pedrorovi/rc-car/platformio/test/embedded/components/test_bt/test_main.cpp

#include <unity.h>

#include <test_utils.h>
#include <tests.h>

int main(void) {
    UNITY_BEGIN();
    RUN_TEST(test_setup);
    RUN_TEST(test_write);
    RUN_TEST(test_read);
    //  Just an indicator that the tests have end.
    UNITY_END();

    while (1)
        flash_leds();
}
