pedrorovi/rc-car/platformio/test/embedded/unity_config.h

#ifndef UNITY_CONFIG_H
#define UNITY_CONFIG_H

#define UNITY_INCLUDE_DOUBLE
#define UNITY_DOUBLE_PRECISION 1e-12

#ifndef NULL

#ifndef __cplusplus
#define NULL (void*)0
#else
#define NULL 0
#endif

#endif

#ifdef __cplusplus
extern "C" {
#endif

void unityOutputStart();
void unityOutputChar(char);
void unityOutputFlush();
void unityOutputComplete();

#define UNITY_OUTPUT_START() unityOutputStart()
#define UNITY_OUTPUT_CHAR(a) unityOutputChar(a)
#define UNITY_OUTPUT_FLUSH() unityOutputFlush()
#define UNITY_OUTPUT_COMPLETE() unityOutputComplete()

#ifdef __cplusplus
}
#endif /* extern "C" */

#endif /* UNITY_CONFIG_H */
